piotr-wiszowaty/yasio/uc/src/led_strip_encoder.h

/*
 * SPDX-FileCopyrightText: 2021-2022 Espressif Systems (Shanghai) CO LTD
 *
 * SPDX-License-Identifier: Apache-2.0
 */
#pragma once

#include <stdint.h>
#include "driver/rmt_encoder.h"

#ifdef __cplusplus
extern "C" {
#endif

/**
 * @brief Create RMT encoder for encoding LED strip pixels into RMT symbols
 *
 * @param[out] ret_encoder Returned encoder handle
 * @return
 *      - ESP_ERR_INVALID_ARG for any invalid arguments
 *      - ESP_ERR_NO_MEM out of memory when creating led strip encoder
 *      - ESP_OK if creating encoder successfully
 */
esp_err_t rmt_new_led_strip_encoder(rmt_encoder_handle_t *ret_encoder);

#ifdef __cplusplus
}
#endif
