piotr-wiszowaty/yasio/uc/src/favicon.h

const char favicon[2273] = {
	0x89, 0x50, 0x4E, 0x47, 0x0D, 0x0A, 0x1A, 0x0A, 0x00, 0x00, 0x00, 0x0D, 0x49, 0x48, 0x44, 0x52, 
	0x00, 0x00, 0x00, 0x20, 0x00, 0x00, 0x00, 0x20, 0x08, 0x06, 0x00, 0x00, 0x00, 0x73, 0x7A, 0x7A, 
	0xF4, 0x00, 0x00, 0x08, 0xA8, 0x49, 0x44, 0x41, 0x54, 0x58, 0x47, 0x55, 0x57, 0x7B, 0x50, 0x5C, 
	0x67, 0x15, 0xFF, 0x7D, 0xF7, 0xB1, 0xB0, 0x2C, 0x41, 0x0B, 0x81, 0xC0, 0xC4, 0x3C, 0xAA, 0x46, 
	0x0A, 0x34, 0x76, 0x42, 0x78, 0x24, 0xC6, 0x46, 0x67, 0x5A, 0xFD, 0x27, 0x71, 0x54, 0x22, 0x4D, 
	0x3B, 0xD3, 0xEA, 0xD8, 0x68, 0xDA, 0x99, 0xD4, 0x40, 0x6D, 0x1D, 0x5B, 0x4B, 0xE9, 0xE8, 0x68, 
	0x63, 0x1A, 0x20, 0x3C, 0xD4, 0x86, 0xA9, 0xDA, 0x98, 0x47, 0x1F, 0x19, 0xC7, 0xE9, 0xC4, 0xC7, 
	0xD4, 0xA9, 0x8D, 0x69, 0x8C, 0x8D, 0x6D, 0x7C, 0x44, 0xD2, 0x00, 0xBB, 0xB0, 0x84, 0xA4, 0xA1, 
	0x34, 0xE4, 0x01, 0x29, 0x2E, 0x2C, 0xBB, 0x77, 0xEF, 0xE7, 0x9C, 0x73, 0xBE, 0xBB, 0xD0, 0x9D, 
	0x81, 0x0B, 0x77, 0xEF, 0x77, 0xBF, 0xDF, 0x39, 0xE7, 0xF7, 0xFB, 0x9D, 0xF3, 0xA9, 0xF1, 0xF1, 
	0x09, 0x0D, 0x05, 0x28, 0x4B, 0x43, 0x29, 0x05, 0xDF, 0xF7, 0xA1, 0x35, 0x00, 0x68, 0x68, 0xAD, 
	0x61, 0x59, 0x16, 0xDF, 0xA3, 0xFF, 0x33, 0x99, 0x0C, 0xDF, 0x03, 0x2D, 0xE0, 0x47, 0x34, 0xA0, 
	0x14, 0xDF, 0xD3, 0x3E, 0x2F, 0x82, 0x2C, 0xD5, 0x72, 0x85, 0x86, 0xA5, 0x14, 0x94, 0x65, 0xC1, 
	0xB6, 0x2C, 0xF0, 0x46, 0xE6, 0x47, 0x6B, 0x1F, 0xB6, 0x65, 0x43, 0x8D, 0x8D, 0xBF, 0xCF, 0xCF, 
	0xBE, 0x7D, 0xFA, 0x14, 0x4E, 0x9E, 0x3A, 0x87, 0xBC, 0x48, 0x04, 0xA5, 0x45, 0x39, 0xB0, 0x6C, 
	0x9B, 0x17, 0x59, 0x96, 0x80, 0x22, 0x70, 0x9A, 0x81, 0x80, 0xBF, 0xA3, 0xFF, 0xE9, 0x7B, 0x02, 
	0x45, 0x7B, 0xA7, 0x52, 0x73, 0xF8, 0xE0, 0xC6, 0x14, 0xE1, 0x81, 0xEB, 0xBA, 0xB0, 0x1D, 0x07, 
	0x8E, 0xE3, 0xC0, 0x75, 0x1D, 0x84, 0x42, 0x39, 0x08, 0xB9, 0x2E, 0xC2, 0x79, 0x11, 0xBE, 0x47, 
	0x3F, 0x9F, 0xF8, 0xF8, 0x2A, 0xE4, 0x86, 0xC3, 0x50, 0x97, 0xC6, 0xC6, 0x35, 0x6D, 0xD2, 0xFB, 
	0xEB, 0x17, 0xB1, 0xEB, 0x0F, 0xB5, 0xF8, 0x7C, 0x75, 0x01, 0x9E, 0x6D, 0x29, 0xC3, 0x95, 0xE9, 
	0x34, 0x0A, 0xF3, 0x5D, 0xE4, 0x38, 0x16, 0xC6, 0x26, 0xD3, 0x48, 0xA5, 0x33, 0xF0, 0x32, 0x1A, 
	0x8B, 0x0B, 0x5C, 0xAC, 0x5A, 0x92, 0xC3, 0x91, 0x50, 0x14, 0x04, 0x84, 0x10, 0x24, 0x66, 0x66, 
	0x51, 0x55, 0xB5, 0x86, 0x01, 0xF1, 0x3D, 0x7E, 0x42, 0xC1, 0xB2, 0x2D, 0xC9, 0x6C, 0xC6, 0x87, 
	0x1B, 0x72, 0x79, 0x73, 0x8A, 0x7C, 0x77, 0xDB, 0xD3, 0x58, 0x57, 0xBF, 0x01, 0x6A, 0xEC, 0x3D, 
	0xCA, 0x80, 0x46, 0xD7, 0xBE, 0x23, 0x68, 0x7B, 0xB5, 0x0E, 0x77, 0xAC, 0x0D, 0xA3, 0xE7, 0xB1, 
	0x32, 0x4C, 0xA7, 0x14, 0x5C, 0x8B, 0x4A, 0x63, 0x21, 0x3F, 0x07, 0x48, 0xCC, 0xFA, 0x08, 0x59, 
	0x19, 0xA4, 0xB4, 0x42, 0xF1, 0x22, 0x87, 0x53, 0xCB, 0xE1, 0xF2, 0x6A, 0x0D, 0x0B, 0x19, 0x54, 
	0x94, 0x57, 0x21, 0x9D, 0x4E, 0xC3, 0x52, 0x94, 0x6E, 0x0D, 0xDB, 0x64, 0x8A, 0x9F, 0x35, 0x60, 
	0x04, 0x80, 0x85, 0x8E, 0xCE, 0x3D, 0xA8, 0xAD, 0x5B, 0x0F, 0x75, 0xF1, 0xDD, 0x31, 0x2E, 0x6B, 
	0x57, 0xEF, 0x11, 0x74, 0xFD, 0x65, 0x1D, 0xBE, 0x58, 0x17, 0xC1, 0xAF, 0x5A, 0xCB, 0x4C, 0xFD, 
	0x1D, 0xE6, 0x00, 0xBD, 0x88, 0x36, 0xE2, 0xE8, 0x4C, 0x9D, 0xA5, 0x1C, 0xC4, 0x1B, 0x0B, 0x80, 
	0x0F, 0xA5, 0x33, 0xA8, 0xAC, 0xB8, 0x15, 0xA9, 0xB9, 0x14, 0x97, 0x99, 0xD6, 0x71, 0x16, 0x94, 
	0xE2, 0xBF, 0x19, 0x02, 0x5D, 0x95, 0x42, 0x28, 0xE4, 0x62, 0x6F, 0x67, 0x1B, 0x6A, 0x6B, 0xD7, 
	0x43, 0x5D, 0xB8, 0x78, 0x89, 0x63, 0xD8, 0xD3, 0xF3, 0x12, 0x7E, 0xF1, 0xC6, 0xED, 0xF8, 0xF2, 
	0xED, 0xF9, 0x38, 0xFC, 0xE3, 0x65, 0xFC, 0x20, 0x2F, 0x56, 0x0E, 0xA3, 0xCF, 0xF8, 0x9E, 0x70, 
	0x0E, 0x94, 0x16, 0xE2, 0x99, 0x86, 0xAF, 0x09, 0x90, 0x40, 0xCA, 0x64, 0x3C, 0xDC, 0xBC, 0xA2, 
	0x1C, 0xA9, 0x54, 0x8A, 0x13, 0x13, 0x94, 0xC1, 0xB2, 0x6C, 0xE6, 0x11, 0xBF, 0xCF, 0x22, 0xDE, 
	0xD8, 0x0C, 0xA4, 0xAB, 0xA7, 0x03, 0x75, 0x04, 0x60, 0xF4, 0xE2, 0x45, 0x06, 0xB0, 0xAB, 0xF3, 
	0x65, 0x3C, 0xF7, 0xF7, 0xCF, 0x61, 0xD3, 0xFA, 0x30, 0x7A, 0x9F, 0x28, 0x93, 0xC8, 0x29, 0x03, 
	0x14, 0x21, 0x6F, 0x08, 0xF8, 0x9E, 0xC7, 0x7F, 0x3B, 0xB6, 0xCD, 0xD9, 0x60, 0x96, 0x13, 0xBB, 
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
};
