piotr-wiszowaty/yasio/uc/src/download_icon.h

const char download_icon[240] = {
	0x89, 0x50, 0x4E, 0x47, 0x0D, 0x0A, 0x1A, 0x0A, 0x00, 0x00, 0x00, 0x0D, 0x49, 0x48, 0x44, 0x52, 
	0x00, 0x00, 0x00, 0x20, 0x00, 0x00, 0x00, 0x20, 0x08, 0x06, 0x00, 0x00, 0x00, 0x73, 0x7A, 0x7A, 
	0xF4, 0x00, 0x00, 0x00, 0xB7, 0x49, 0x44, 0x41, 0x54, 0x58, 0x47, 0xED, 0x96, 0x51, 0x0A, 0x84, 
	0x30, 0x0C, 0x44, 0xF5, 0xFE, 0x87, 0x56, 0x0A, 0xBB, 0x52, 0xB2, 0x13, 0x3B, 0xB1, 0x33, 0xE0, 
	0x42, 0xDF, 0xA7, 0x68, 0xF3, 0x92, 0x90, 0x9A, 0x7D, 0xFB, 0xE5, 0x00, 0xCF, 0x2A, 0xEC, 0x33, 
	0x2F, 0xCF, 0x06, 0xFF, 0x42, 0x4B, 0xF4, 0x2F, 0xAA, 0x82, 0x97, 0x24, 0x32, 0x01, 0x3A, 0x83, 
	0x0F, 0x99, 0xFC, 0xF0, 0x1C, 0xB7, 0x40, 0xE3, 0x56, 0xC2, 0x21, 0xD0, 0xCE, 0x8C, 0x15, 0x49, 
	0x25, 0x5C, 0x02, 0x0D, 0x4A, 0xC2, 0x29, 0x40, 0x49, 0xB8, 0x05, 0x86, 0x12, 0x0E, 0x01, 0x86, 
	0x2B, 0xEE, 0x12, 0x50, 0x55, 0x80, 0xA1, 0x9F, 0x0A, 0x79, 0x0B, 0x18, 0xE4, 0x02, 0xD4, 0x9C, 
	0x77, 0x2C, 0x81, 0x55, 0x81, 0xFF, 0xAF, 0x40, 0xCC, 0x00, 0x4D, 0x01, 0xCC, 0x12, 0x2C, 0x2D, 
	0x8F, 0xEE, 0x81, 0xEA, 0xCA, 0x16, 0x77, 0x00, 0x49, 0x0B, 0x58, 0x09, 0xB4, 0x80, 0x48, 0x04, 
	0xD0, 0xEF, 0x35, 0x82, 0x82, 0xC7, 0xEF, 0x1E, 0xB5, 0x20, 0xBB, 0xD5, 0x7A, 0xB2, 0xE0, 0x72, 
	0x81, 0xE1, 0xA2, 0x01, 0x90, 0xB5, 0x00, 0x55, 0xE2, 0x2E, 0x73, 0xD9, 0x14, 0xCC, 0x62, 0xA9, 
	0x40, 0x85, 0x92, 0x80, 0x9B, 0xE1, 0x14, 0xB8, 0x79, 0x8F, 0xC0, 0x09, 0x72, 0x5B, 0x4D, 0x21, 
	0xEF, 0x93, 0xAC, 0xBC, 0x00, 0x00, 0x00, 0x00, 0x49, 0x45, 0x4E, 0x44, 0xAE, 0x42, 0x60, 0x82
};
