piotr-wiszowaty/yasio/uc/src/eject_icon.h

const char eject_icon[324] = {
	0x89, 0x50, 0x4E, 0x47, 0x0D, 0x0A, 0x1A, 0x0A, 0x00, 0x00, 0x00, 0x0D, 0x49, 0x48, 0x44, 0x52, 
	0x00, 0x00, 0x00, 0x20, 0x00, 0x00, 0x00, 0x20, 0x08, 0x06, 0x00, 0x00, 0x00, 0x73, 0x7A, 0x7A, 
	0xF4, 0x00, 0x00, 0x01, 0x0A, 0x49, 0x44, 0x41, 0x54, 0x58, 0x47, 0xED, 0x95, 0x3D, 0x0E, 0x44, 
	0x40, 0x18, 0x86, 0x5F, 0x95, 0x03, 0xB8, 0x80, 0x03, 0xB8, 0x80, 0x48, 0x68, 0x14, 0x0A, 0xA5, 
	0x4E, 0x43, 0xE5, 0x4E, 0x14, 0x9C, 0x80, 0x42, 0xA9, 0x51, 0x29, 0x1C, 0xC1, 0x1D, 0x5C, 0x40, 
	0xB3, 0x1B, 0x93, 0x10, 0x3F, 0xBB, 0x36, 0xC6, 0xCC, 0xDA, 0x4D, 0xE6, 0x69, 0x27, 0xBC, 0x4F, 
	0x5E, 0xF3, 0x7D, 0x24, 0x00, 0x0F, 0xDC, 0x88, 0xB4, 0x15, 0x28, 0x8A, 0x02, 0x96, 0x65, 0x11, 
	0xA5, 0xB6, 0x6D, 0xE1, 0x38, 0x0E, 0x57, 0xBD, 0x9D, 0x40, 0x55, 0x55, 0xB0, 0x6D, 0x9B, 0x84, 
	0x36, 0x4D, 0x03, 0xC3, 0x30, 0x84, 0x00, 0xFF, 0x06, 0x82, 0x20, 0x98, 0x43, 0x7C, 0xDF, 0x5F, 
	0x7D, 0x82, 0x24, 0x49, 0xE6, 0xB3, 0x2C, 0xCB, 0x98, 0xCB, 0x90, 0x3B, 0x30, 0x0A, 0xA4, 0x69, 
	0x7A, 0xF8, 0xF2, 0x30, 0x0C, 0xF9, 0x09, 0x8C, 0xC9, 0x9A, 0xA6, 0xA1, 0x2C, 0x4B, 0xA8, 0xAA, 
	0xBA, 0x12, 0x19, 0x86, 0x01, 0x51, 0x14, 0x71, 0x09, 0x1F, 0x59, 0x4D, 0x81, 0xA2, 0x28, 0xC8, 
	0xF3, 0x1C, 0xA6, 0x69, 0x92, 0xC3, 0xBE, 0xEF, 0xE1, 0x79, 0x1E, 0xEA, 0xBA, 0x66, 0x5E, 0xFD, 
	0xC4, 0x6E, 0x0C, 0x65, 0x59, 0x46, 0x1C, 0xC7, 0xD0, 0x75, 0x1D, 0xAE, 0xEB, 0xA2, 0xEB, 0x3A, 
	0x6E, 0xE1, 0xBB, 0x06, 0xEE, 0x60, 0xD7, 0xC0, 0xB7, 0xB9, 0x22, 0x30, 0x3E, 0xBB, 0x84, 0xEA, 
	0x9F, 0x42, 0x2B, 0xB0, 0x0D, 0x9F, 0x38, 0x2D, 0x41, 0x23, 0xF0, 0x2E, 0x9C, 0x4A, 0x42, 0x08, 
	0xFC, 0x65, 0x03, 0xD3, 0xFE, 0x78, 0xC5, 0x57, 0x2E, 0xE1, 0x72, 0x8B, 0xDE, 0x36, 0x86, 0xCC, 
	0x60, 0xB2, 0x4C, 0xAE, 0x20, 0x04, 0x7E, 0xA2, 0x81, 0xD3, 0xA3, 0xB3, 0xE0, 0xD3, 0x5A, 0x3E, 
	0x82, 0xE4, 0xD2, 0x2C, 0x22, 0x21, 0x20, 0x1A, 0x60, 0xCA, 0xD5, 0x4B, 0x78, 0x99, 0x27, 0xBF, 
	0xBA, 0x6C, 0x01, 0x6D, 0x69, 0x85, 0xA1, 0x00, 0x00, 0x00, 0x00, 0x49, 0x45, 0x4E, 0x44, 0xAE, 
	0x42, 0x60, 0x82, 0x00
};
