piotr-wiszowaty/yasio/uc/src/insert_icon.h

const char insert_icon[327] = {
	0x89, 0x50, 0x4E, 0x47, 0x0D, 0x0A, 0x1A, 0x0A, 0x00, 0x00, 0x00, 0x0D, 0x49, 0x48, 0x44, 0x52, 
	0x00, 0x00, 0x00, 0x20, 0x00, 0x00, 0x00, 0x20, 0x08, 0x06, 0x00, 0x00, 0x00, 0x73, 0x7A, 0x7A, 
	0xF4, 0x00, 0x00, 0x01, 0x0E, 0x49, 0x44, 0x41, 0x54, 0x58, 0x47, 0xED, 0x95, 0x3F, 0xEE, 0x44, 
	0x40, 0x00, 0x85, 0xDF, 0x54, 0xA2, 0x76, 0x01, 0x07, 0x70, 0x01, 0x91, 0xD0, 0x28, 0x14, 0x4A, 
	0x9D, 0x86, 0xCA, 0x9D, 0x28, 0x38, 0x01, 0x85, 0x52, 0xA3, 0x52, 0x38, 0x82, 0x3B, 0x68, 0x15, 
	0x9A, 0xDF, 0x2F, 0x3B, 0x09, 0x61, 0xED, 0xDF, 0x61, 0xD6, 0x6E, 0x32, 0x5F, 0x27, 0x22, 0xEF, 
	0xCB, 0x33, 0x1E, 0x02, 0xE0, 0x0F, 0x27, 0x42, 0x6E, 0x09, 0x10, 0x42, 0x20, 0xCB, 0x32, 0x86, 
	0x61, 0xE0, 0xAE, 0xB6, 0x11, 0x90, 0x24, 0x09, 0x71, 0x1C, 0x43, 0xD7, 0x75, 0xB8, 0xAE, 0x8B, 
	0xAE, 0xEB, 0xB8, 0x4A, 0xAC, 0x04, 0x14, 0x45, 0x41, 0x9E, 0xE7, 0x30, 0x4D, 0x93, 0x86, 0xF6, 
	0x7D, 0x0F, 0xCF, 0xF3, 0x50, 0xD7, 0x35, 0x37, 0x89, 0x59, 0x40, 0xD3, 0x34, 0x94, 0x65, 0x09, 
	0x55, 0x55, 0x57, 0x61, 0xE3, 0x38, 0x22, 0x8A, 0x22, 0x64, 0x59, 0xC6, 0x45, 0x82, 0x0A, 0x04, 
	0x41, 0x80, 0x34, 0x4D, 0x1F, 0x06, 0x84, 0x61, 0xC8, 0x45, 0x62, 0x16, 0x98, 0xF0, 0x7D, 0x1F, 
	0xB6, 0x6D, 0xD3, 0xCB, 0xA6, 0x69, 0x90, 0x24, 0xC9, 0x7C, 0x8F, 0x47, 0x0B, 0x9B, 0x43, 0x58, 
	0x55, 0xD5, 0x4A, 0xC0, 0x30, 0x0C, 0x2E, 0xD5, 0x4F, 0x08, 0x81, 0x4D, 0x03, 0x45, 0x51, 0xC0, 
	0xB2, 0x2C, 0xDA, 0x50, 0xDB, 0xB6, 0x70, 0x1C, 0xE7, 0xB3, 0xAF, 0xE0, 0xD3, 0xDC, 0x9C, 0xE2, 
	0x17, 0xB9, 0x3C, 0xBB, 0x84, 0xE9, 0x9F, 0xC2, 0x2A, 0x70, 0x1D, 0x3E, 0xF1, 0xB6, 0x04, 0x8B, 
	0xC0, 0xBD, 0x70, 0x26, 0x09, 0x21, 0xF0, 0x93, 0x0D, 0x5C, 0x38, 0xF5, 0x10, 0x2E, 0x67, 0xFC, 
	0xB4, 0xCF, 0xF0, 0x30, 0x0E, 0x19, 0x93, 0x3D, 0x08, 0x81, 0xAF, 0x68, 0xE0, 0xED, 0xFD, 0x5E, 
	0xF0, 0x6C, 0x96, 0x1F, 0x41, 0x73, 0x59, 0x86, 0x48, 0x08, 0x88, 0x06, 0x0E, 0x65, 0xEF, 0x21, 
	0xDC, 0xCD, 0x3F, 0xA4, 0x00, 0x6F, 0x01, 0xB4, 0x64, 0x4E, 0x72, 0x00, 0x00, 0x00, 0x00, 0x49, 
	0x45, 0x4E, 0x44, 0xAE, 0x42, 0x60, 0x82
};
