piotr-wiszowaty/yasio/uc/src/mkdir_icon.h

const char mkdir_icon[204] = {
	0x89, 0x50, 0x4E, 0x47, 0x0D, 0x0A, 0x1A, 0x0A, 0x00, 0x00, 0x00, 0x0D, 0x49, 0x48, 0x44, 0x52, 
	0x00, 0x00, 0x00, 0x20, 0x00, 0x00, 0x00, 0x20, 0x08, 0x06, 0x00, 0x00, 0x00, 0x73, 0x7A, 0x7A, 
	0xF4, 0x00, 0x00, 0x00, 0x91, 0x49, 0x44, 0x41, 0x54, 0x58, 0x47, 0xED, 0x96, 0x5B, 0x0A, 0x80, 
	0x30, 0x0C, 0x04, 0xED, 0xFD, 0x0F, 0xAD, 0x44, 0x48, 0x69, 0x8B, 0x0F, 0x36, 0xBB, 0x18, 0x84, 
	0xCC, 0x7F, 0xD3, 0x71, 0x35, 0x31, 0x6D, 0x4B, 0xA6, 0x25, 0xDF, 0xDF, 0x05, 0x76, 0x42, 0x84, 
	0x7A, 0x08, 0x3B, 0xCC, 0x5C, 0xEE, 0x84, 0x25, 0x54, 0x02, 0x46, 0x48, 0x62, 0x15, 0x40, 0x8A, 
	0x5C, 0x25, 0x87, 0x9C, 0xEF, 0xD6, 0x63, 0x21, 0xB4, 0x00, 0xFB, 0xFA, 0x1A, 0x93, 0x80, 0x43, 
	0x49, 0x28, 0x04, 0x8C, 0xB0, 0x84, 0x4A, 0x00, 0x61, 0x92, 0xCD, 0x10, 0x98, 0x12, 0x63, 0x04, 
	0x24, 0x1F, 0x6F, 0x09, 0xFC, 0x2A, 0x01, 0xA4, 0xD5, 0xDE, 0x06, 0x5A, 0xAF, 0x85, 0x24, 0x50, 
	0x02, 0x2B, 0xD5, 0x86, 0x95, 0x00, 0x43, 0xA8, 0x0D, 0x95, 0xDC, 0x0A, 0x84, 0x77, 0x3B, 0x80, 
	0xC7, 0xDF, 0xF1, 0xE7, 0x28, 0xB7, 0xE2, 0x10, 0x3E, 0xB3, 0x91, 0x31, 0xAB, 0xE4, 0x5C, 0x4A, 
	0x53, 0x29, 0x81, 0xF4, 0x04, 0x0E, 0x9F, 0xE7, 0x39, 0x0D, 0x07, 0x7B, 0x9F, 0x46, 0x00, 0x00, 
	0x00, 0x00, 0x49, 0x45, 0x4E, 0x44, 0xAE, 0x42, 0x60, 0x82, 0x00, 0x00
};
