piotr-wiszowaty/yasio/uc/src/new_image_icon.h

const char new_image_icon[204] = {
	0x89, 0x50, 0x4E, 0x47, 0x0D, 0x0A, 0x1A, 0x0A, 0x00, 0x00, 0x00, 0x0D, 0x49, 0x48, 0x44, 0x52, 
	0x00, 0x00, 0x00, 0x20, 0x00, 0x00, 0x00, 0x20, 0x08, 0x06, 0x00, 0x00, 0x00, 0x73, 0x7A, 0x7A, 
	0xF4, 0x00, 0x00, 0x00, 0x91, 0x49, 0x44, 0x41, 0x54, 0x58, 0x47, 0xED, 0x96, 0x5B, 0x0A, 0xC0, 
	0x20, 0x0C, 0x04, 0xEB, 0xFD, 0x0F, 0xDD, 0x12, 0x68, 0x8B, 0xD8, 0xA8, 0x1B, 0x92, 0x2D, 0x7D, 
	0x64, 0x3E, 0x45, 0xCC, 0xB8, 0x1A, 0xB4, 0x2C, 0x57, 0x56, 0x65, 0xCC, 0x42, 0xF1, 0x4C, 0xF6, 
	0x16, 0x3F, 0x80, 0x25, 0xEA, 0x89, 0x51, 0xC5, 0x4D, 0x12, 0x3D, 0x01, 0x78, 0x07, 0x3B, 0x3D, 
	0xF9, 0xE9, 0x3A, 0x6C, 0x01, 0x61, 0x28, 0xC1, 0x10, 0x90, 0x35, 0xDB, 0x44, 0xBA, 0x12, 0x2C, 
	0x01, 0x01, 0x92, 0x60, 0x0A, 0x40, 0x12, 0x6C, 0x81, 0xA9, 0x04, 0x43, 0x00, 0xE1, 0xAC, 0x9B, 
	0x02, 0x51, 0x09, 0x20, 0xD4, 0x5D, 0x11, 0x7E, 0x04, 0x08, 0xDF, 0x13, 0x50, 0x77, 0x34, 0x20, 
	0x3C, 0x81, 0x14, 0xB8, 0x3D, 0x01, 0xCB, 0x87, 0x45, 0x7B, 0xFD, 0xDC, 0x77, 0x20, 0x05, 0x5A, 
	0xD4, 0x48, 0xB3, 0x0D, 0x7F, 0x95, 0x80, 0x15, 0x77, 0x1B, 0x7A, 0x79, 0x97, 0x00, 0x9B, 0xE9, 
	0x87, 0x84, 0xCD, 0x73, 0x04, 0x36, 0x41, 0x4E, 0x49, 0x21, 0x00, 0x2F, 0x97, 0x24, 0x00, 0x00, 
	0x00, 0x00, 0x49, 0x45, 0x4E, 0x44, 0xAE, 0x42, 0x60, 0x82, 0x00, 0x00
};
