piotr-wiszowaty/yasio/uc/src/reload_icon.h

const char reload_icon[297] = {
	0x89, 0x50, 0x4E, 0x47, 0x0D, 0x0A, 0x1A, 0x0A, 0x00, 0x00, 0x00, 0x0D, 0x49, 0x48, 0x44, 0x52, 
	0x00, 0x00, 0x00, 0x20, 0x00, 0x00, 0x00, 0x20, 0x08, 0x06, 0x00, 0x00, 0x00, 0x73, 0x7A, 0x7A, 
	0xF4, 0x00, 0x00, 0x00, 0xEE, 0x49, 0x44, 0x41, 0x54, 0x58, 0x47, 0xED, 0x96, 0x4B, 0x0E, 0xC4, 
	0x20, 0x0C, 0x43, 0x87, 0xFB, 0x1F, 0x7A, 0x2A, 0x90, 0xA8, 0xF8, 0x24, 0xD8, 0x09, 0x61, 0xD8, 
	0xCC, 0x5B, 0x53, 0xDB, 0x24, 0x0D, 0x90, 0x3E, 0x76, 0xBE, 0xE0, 0x93, 0x64, 0x91, 0x64, 0x17, 
	0x23, 0x53, 0x0D, 0x4D, 0xBF, 0xEA, 0x25, 0x14, 0xC0, 0x6B, 0x3C, 0xD2, 0xFA, 0xB4, 0x9A, 0xCB, 
	0x00, 0x51, 0xE6, 0x95, 0x1C, 0x62, 0xD4, 0x54, 0x03, 0x20, 0x73, 0x54, 0x5A, 0x16, 0x31, 0x80, 
	0x66, 0x8E, 0xDA, 0x35, 0x82, 0x36, 0x91, 0x99, 0x02, 0x44, 0x99, 0x57, 0x50, 0x08, 0x2A, 0x80, 
	0x75, 0xE7, 0x2D, 0xA6, 0x00, 0xD2, 0xE2, 0x93, 0xE6, 0x5D, 0x0B, 0x6E, 0x98, 0x2F, 0x03, 0x9C, 
	0xDE, 0xF9, 0x3B, 0x9A, 0xD5, 0x68, 0x9A, 0x4F, 0x76, 0x8E, 0x04, 0x50, 0xDF, 0x5B, 0x4A, 0x80, 
	0xE8, 0xF2, 0x9B, 0x10, 0x4F, 0x27, 0x93, 0xC2, 0x26, 0xFF, 0x00, 0xB7, 0x2A, 0xD0, 0x5D, 0xC7, 
	0x91, 0x13, 0xC0, 0xD0, 0xF9, 0xDD, 0xA8, 0x00, 0x0C, 0x50, 0x4E, 0x28, 0x66, 0x2B, 0x0E, 0xA6, 
	0x91, 0x3F, 0x71, 0x10, 0xAD, 0x50, 0x1F, 0x24, 0xBF, 0xFA, 0x0F, 0xE8, 0x00, 0x27, 0xDA, 0x20, 
	0x9E, 0xB8, 0xDA, 0x63, 0xF1, 0xBD, 0x2C, 0x1C, 0x7D, 0x66, 0xEF, 0x87, 0xA2, 0x3D, 0x1A, 0x9C, 
	0xB8, 0x17, 0x96, 0xAF, 0x2C, 0x26, 0xC0, 0x4E, 0x3B, 0xE0, 0x13, 0x4F, 0x2A, 0x31, 0xFC, 0x88, 
	0x84, 0xD2, 0xF1, 0x3E, 0xAF, 0xC3, 0xBE, 0xD3, 0x84, 0x32, 0xDA, 0x0E, 0xBC, 0x88, 0x5E, 0xAB, 
	0x00, 0x95, 0x88, 0x20, 0xAA, 0x0F, 0x13, 0x60, 0xA7, 0x1A, 0x50, 0x1F, 0x2E, 0x10, 0x40, 0x15, 
	0x31, 0x69, 0x3E, 0x7B, 0xAF, 0x37, 0x1E, 0x74, 0x59, 0xD4, 0xF7, 0x00, 0x00, 0x00, 0x00, 0x49, 
	0x45, 0x4E, 0x44, 0xAE, 0x42, 0x60, 0x82, 0x00, 0x00
};
