piotr-wiszowaty/yasio/uc/src/trash_icon.h

const char trash_icon[195] = {
	0x89, 0x50, 0x4E, 0x47, 0x0D, 0x0A, 0x1A, 0x0A, 0x00, 0x00, 0x00, 0x0D, 0x49, 0x48, 0x44, 0x52, 
	0x00, 0x00, 0x00, 0x20, 0x00, 0x00, 0x00, 0x20, 0x08, 0x06, 0x00, 0x00, 0x00, 0x73, 0x7A, 0x7A, 
	0xF4, 0x00, 0x00, 0x00, 0x88, 0x49, 0x44, 0x41, 0x54, 0x58, 0x47, 0xED, 0x97, 0x51, 0x0A, 0xC0, 
	0x20, 0x0C, 0x43, 0xE7, 0xFD, 0x0F, 0xBD, 0x21, 0x8C, 0x21, 0xAE, 0x2D, 0x89, 0x76, 0x28, 0x23, 
	0xEF, 0xD7, 0xA2, 0x49, 0x2C, 0x52, 0xCB, 0xB1, 0x98, 0x42, 0x9C, 0x7F, 0x12, 0xB5, 0x15, 0x68, 
	0x6F, 0xA8, 0xE8, 0x66, 0x2B, 0x01, 0x9E, 0xF0, 0x56, 0x24, 0x64, 0x0E, 0x2A, 0x32, 0x12, 0xF8, 
	0x4C, 0x00, 0x1B, 0xF3, 0x28, 0x8F, 0x81, 0xDE, 0x89, 0x04, 0x30, 0xF7, 0x8D, 0x12, 0x36, 0x66, 
	0x5A, 0x33, 0x05, 0x48, 0xC0, 0xFF, 0x12, 0xB0, 0x1C, 0x45, 0x2E, 0xA3, 0xB5, 0xA1, 0x26, 0x94, 
	0x00, 0x25, 0xA0, 0x04, 0x94, 0x80, 0x12, 0x60, 0x49, 0x7F, 0x8A, 0x59, 0x24, 0x60, 0x3A, 0x01, 
	0xF8, 0x9B, 0x65, 0xD0, 0x4F, 0xD9, 0xAF, 0x11, 0x10, 0x99, 0x09, 0x33, 0x81, 0x05, 0x54, 0xB2, 
	0xFF, 0x08, 0xA6, 0x59, 0x2F, 0x01, 0x6B, 0x3C, 0x9F, 0xC1, 0x3D, 0xE7, 0x02, 0xE8, 0x8B, 0x4C, 
	0x21, 0xB6, 0x6B, 0xDB, 0x72, 0x00, 0x00, 0x00, 0x00, 0x49, 0x45, 0x4E, 0x44, 0xAE, 0x42, 0x60, 
	0x82, 0x00, 0x00
};
