piotr-wiszowaty/yasio/uc/src/upload_icon.h

const char upload_icon[237] = {
	0x89, 0x50, 0x4E, 0x47, 0x0D, 0x0A, 0x1A, 0x0A, 0x00, 0x00, 0x00, 0x0D, 0x49, 0x48, 0x44, 0x52, 
	0x00, 0x00, 0x00, 0x20, 0x00, 0x00, 0x00, 0x20, 0x08, 0x06, 0x00, 0x00, 0x00, 0x73, 0x7A, 0x7A, 
	0xF4, 0x00, 0x00, 0x00, 0xB3, 0x49, 0x44, 0x41, 0x54, 0x58, 0x47, 0xED, 0x96, 0xE1, 0x0A, 0x80, 
	0x20, 0x0C, 0x84, 0xF3, 0xFD, 0x1F, 0xBA, 0x10, 0x32, 0xC4, 0x9C, 0xBB, 0xE1, 0x1D, 0x19, 0xF8, 
	0xFD, 0x0C, 0xD9, 0x7D, 0xCD, 0x9C, 0xA5, 0xE3, 0xCD, 0xD9, 0x79, 0x16, 0x21, 0xCD, 0x2C, 0x9E, 
	0x0D, 0x2F, 0xC0, 0x12, 0xF5, 0x42, 0x56, 0x78, 0x48, 0xC2, 0x12, 0x80, 0xDF, 0xE0, 0xC6, 0x92, 
	0x77, 0xEB, 0xA8, 0x05, 0x32, 0x43, 0x09, 0x85, 0x40, 0xAE, 0xD9, 0x76, 0xC4, 0x94, 0x50, 0x09, 
	0x64, 0x20, 0x09, 0xA5, 0x00, 0x24, 0xA1, 0x16, 0x70, 0x25, 0x14, 0x02, 0x08, 0x4F, 0xEE, 0x16, 
	0x60, 0x75, 0x00, 0xA1, 0x3E, 0x15, 0xF4, 0x2D, 0x40, 0x90, 0x08, 0x94, 0xA2, 0xEE, 0xC8, 0x6D, 
	0xE6, 0x02, 0xA5, 0x03, 0xD0, 0xA0, 0xA9, 0xA0, 0x76, 0xA0, 0x0D, 0x47, 0x6E, 0x40, 0x9A, 0x80, 
	0x15, 0xEE, 0x49, 0x50, 0x04, 0xBC, 0xF0, 0x91, 0xC4, 0xB4, 0x00, 0x1A, 0x6E, 0x49, 0x50, 0x05, 
	0xAC, 0x2B, 0xB7, 0x1B, 0xD2, 0xF9, 0x69, 0xF9, 0xFF, 0x29, 0x70, 0x6F, 0xB9, 0x0E, 0xD3, 0x5B, 
	0xD0, 0xF2, 0xE9, 0x1C, 0xD8, 0x1D, 0x58, 0xA2, 0x03, 0x51, 0xE8, 0x1F, 0x61, 0x94, 0x90, 0x80, 
	0x1A, 0x77, 0x10, 0xA9, 0x59, 0x47, 0xE0, 0x02, 0x72, 0x5B, 0x4D, 0x21, 0xDE, 0x7D, 0x38, 0xBD, 
	0x00, 0x00, 0x00, 0x00, 0x49, 0x45, 0x4E, 0x44, 0xAE, 0x42, 0x60, 0x82, 0x00
};
