piotr-wiszowaty/yasio/uc/src/bootloader_hs.h

uint8_t bootloader_hs[1024] = {
	0x00, 0x03, 0x00, 0x07, 0x00, 0x00, 0x4C, 0x5D, 0x07, 0x01, 0x00, 0x00, 0x00, 0x00, 0x00, 0x00, 
	0x00, 0x00, 0x00, 0x00, 0x4C, 0x6F, 0x61, 0x64, 0x69, 0x6E, 0x67, 0x20, 0x00, 0x00, 0x00, 0x00, 
	0x00, 0x00, 0x00, 0x00, 0x00, 0x00, 0x00, 0x00, 0x00, 0x00, 0x00, 0x00, 0x00, 0x00, 0x00, 0x00, 
	0x00, 0x00, 0x00, 0x00, 0x00, 0x00, 0x00, 0x00, 0x00, 0x00, 0x00, 0x00, 0x9B, 0x00, 0x00, 0x00, 
	0x00, 0x00, 0x00, 0x0A, 0x00, 0x00, 0x60, 0xA2, 0x00, 0x9D, 0x44, 0x03, 0x98, 0x9D, 0x45, 0x03, 
	0xA9, 0xFF, 0x9D, 0x48, 0x03, 0xA9, 0x09, 0x9D, 0x42, 0x03, 0x4C, 0x56, 0xE4, 0xA9, 0x31, 0x8D, 
	0x00, 0x03, 0xA9, 0x01, 0x8D, 0x01, 0x03, 0xA9, 0x08, 0x8D, 0x06, 0x03, 0xA9, 0x80, 0x8D, 0x04, 
	0x03, 0xA9, 0x08, 0x8D, 0x05, 0x03, 0xA9, 0x80, 0x8D, 0x08, 0x03, 0xA9, 0x00, 0x8D, 0x09, 0x03, 
	0xA9, 0x04, 0x8D, 0x0A, 0x03, 0xA9, 0x00, 0x8D, 0x0B, 0x03, 0xA9, 0x52, 0x8D, 0x02, 0x03, 0xA9, 
	0x40, 0x8D, 0x03, 0x03, 0x20, 0x59, 0xE4, 0x30, 0xF6, 0x18, 0xAD, 0x04, 0x03, 0x69, 0x80, 0x8D, 
	0x04, 0x03, 0xAD, 0x05, 0x03, 0x69, 0x00, 0x8D, 0x05, 0x03, 0xEE, 0x0A, 0x03, 0xAD, 0x0A, 0x03, 
	0xC9, 0x09, 0xD0, 0xDB, 0xA9, 0x14, 0xA0, 0x07, 0x20, 0x47, 0x07, 0xA9, 0x40, 0x8D, 0x03, 0x03, 
	0xA9, 0x43, 0x8D, 0x04, 0x03, 0xA9, 0x07, 0x8D, 0x05, 0x03, 0xA9, 0x01, 0x8D, 0x08, 0x03, 0xA9, 
	0x00, 0x8D, 0x09, 0x03, 0xA9, 0x3F, 0x8D, 0x02, 0x03, 0x20, 0x59, 0xE4, 0x20, 0x2F, 0x09, 0x20, 
	0x45, 0x09, 0xA9, 0x00, 0x8D, 0xE0, 0x02, 0x8D, 0xE1, 0x02, 0xA9, 0xF9, 0x8D, 0x02, 0x03, 0xA9, 
	0x3D, 0x8D, 0x04, 0x03, 0xA9, 0x07, 0x8D, 0x05, 0x03, 0xA9, 0x04, 0x8D, 0x08, 0x03, 0xA9, 0x00, 
	0x8D, 0x09, 0x03, 0x20, 0x6B, 0x09, 0x10, 0x05, 0xA9, 0xF8, 0x4C, 0xEC, 0x07, 0xA9, 0xFF, 0xCD, 
	0x3D, 0x07, 0xD0, 0x29, 0xCD, 0x3E, 0x07, 0xD0, 0x24, 0xCD, 0x3F, 0x07, 0xD0, 0x1F, 0xCD, 0x40, 
	0x07, 0xD0, 0x1A, 0xAD, 0xE0, 0x02, 0x0D, 0xE1, 0x02, 0xD0, 0x0C, 0xAD, 0x44, 0x07, 0x8D, 0xE0, 
	0x02, 0xAD, 0x45, 0x07, 0x8D, 0xE1, 0x02, 0x20, 0x36, 0x09, 0x6C, 0xE0, 0x02, 0xA9, 0xFF, 0xCD, 
	0x3D, 0x07, 0xD0, 0x34, 0xCD, 0x3E, 0x07, 0xD0, 0x2F, 0xAD, 0x3F, 0x07, 0x8D, 0x3D, 0x07, 0xAD, 
	0x40, 0x07, 0x8D, 0x3E, 0x07, 0xA9, 0xF9, 0x8D, 0x02, 0x03, 0xA9, 0x3F, 0x8D, 0x04, 0x03, 0xA9, 
	0x07, 0x8D, 0x05, 0x03, 0xA9, 0x02, 0x8D, 0x08, 0x03, 0xA9, 0x00, 0x8D, 0x09, 0x03, 0x20, 0x6B, 
	0x09, 0x10, 0x05, 0xA9, 0xF8, 0x4C, 0x57, 0x08, 0xAD, 0x44, 0x07, 0x0D, 0x45, 0x07, 0xD0, 0x0C, 
	0xAD, 0x3D, 0x07, 0x8D, 0x44, 0x07, 0xAD, 0x3E, 0x07, 0x8D, 0x45, 0x07, 0xA9, 0x46, 0x8D, 0xE2, 
	0x02, 0xA9, 0x07, 0x8D, 0xE3, 0x02, 0x38, 0xAD, 0x3F, 0x07, 0xED, 0x3D, 0x07, 0xAD, 0x40, 0x07, 
	0xED, 0x3E, 0x07, 0xB0, 0x12, 0x20, 0x36, 0x09, 0x20, 0xB4, 0x08, 0x20, 0x2F, 0x09, 0x20, 0x45, 
	0x09, 0x4C, 0xEA, 0x07, 0x6C, 0xE2, 0x02, 0x38, 0xAD, 0x3F, 0x07, 0xED, 0x3D, 0x07, 0x8D, 0x41, 
	0x07, 0xAD, 0x40, 0x07, 0xED, 0x3E, 0x07, 0x8D, 0x42, 0x07, 0x18, 0xA9, 0x01, 0x6D, 0x41, 0x07, 
	0x8D, 0x41, 0x07, 0xA9, 0x00, 0x6D, 0x42, 0x07, 0x8D, 0x42, 0x07, 0x38, 0xA9, 0x00, 0xED, 0x41, 
	0x07, 0xA9, 0x02, 0xED, 0x42, 0x07, 0xB0, 0x0A, 0xA9, 0x00, 0x8D, 0x41, 0x07, 0xA9, 0x02, 0x8D, 
	0x42, 0x07, 0xA9, 0xF9, 0x8D, 0x02, 0x03, 0xAD, 0x3D, 0x07, 0x8D, 0x04, 0x03, 0xAD, 0x3E, 0x07, 
	0x8D, 0x05, 0x03, 0xAD, 0x41, 0x07, 0x8D, 0x08, 0x03, 0xAD, 0x42, 0x07, 0x8D, 0x09, 0x03, 0x20, 
	0x6B, 0x09, 0x10, 0x05, 0xA9, 0xF8, 0x4C, 0xF4, 0x08, 0x18, 0xAD, 0x41, 0x07, 0x6D, 0x3D, 0x07, 
	0x8D, 0x3D, 0x07, 0xAD, 0x42, 0x07, 0x6D, 0x3E, 0x07, 0x8D, 0x3E, 0x07, 0x4C, 0x96, 0x08, 0x78, 
	0xA9, 0x00, 0x8D, 0x0E, 0xD4, 0x60, 0xA5, 0x10, 0x8D, 0x0E, 0xD2, 0xA9, 0x40, 0x8D, 0x0E, 0xD4, 
	0x58, 0x8D, 0x0A, 0xD4, 0x60, 0xA9, 0x00, 0x8D, 0x0E, 0xD2, 0xAD, 0x43, 0x07, 0x8D, 0x04, 0xD2, 
	0xA9, 0x00, 0x8D, 0x06, 0xD2, 0xA9, 0x28, 0x8D, 0x08, 0xD2, 0xA9, 0xA0, 0x8D, 0x01, 0xD2, 0x8D, 
	0x03, 0xD2, 0x8D, 0x05, 0xD2, 0xA9, 0xA8, 0x8D, 0x07, 0xD2, 0x60, 0xAD, 0x08, 0x03, 0x8D, 0x0A, 
	0x03, 0xAD, 0x09, 0x03, 0x8D, 0x0B, 0x03, 0xA9, 0x40, 0x8D, 0x03, 0x03, 0xA9, 0x00, 0x8D, 0x0E, 
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
};
